alexavoicu/TSC-Proiect/Images/Baterie1.png

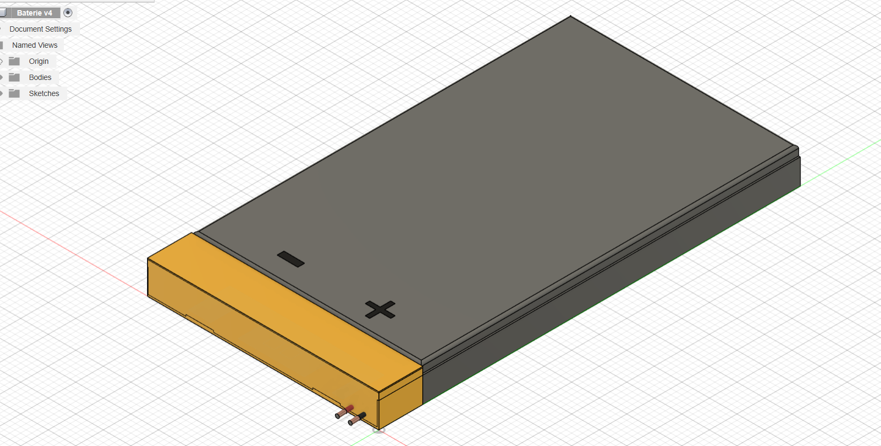
Images/Baterie1.png
