alexavoicu/TSC-Proiect/Images/Baterie2.png

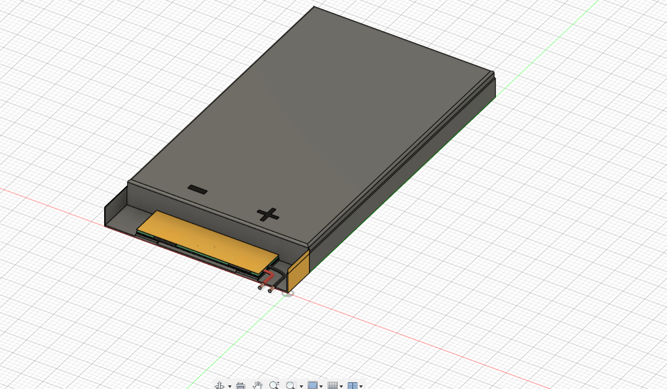
Images/Baterie2.png
