alexavoicu/TSC-Proiect/Images/Openbook2.png

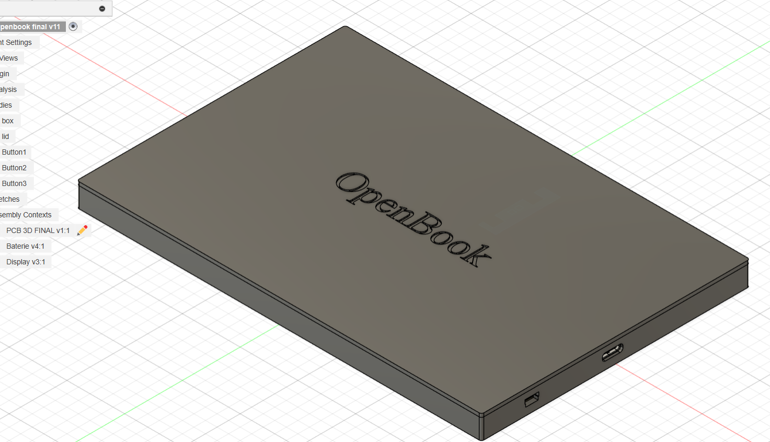
Images/Openbook2.png
