alexavoicu/TSC-Proiect/Images/Openbook3.png

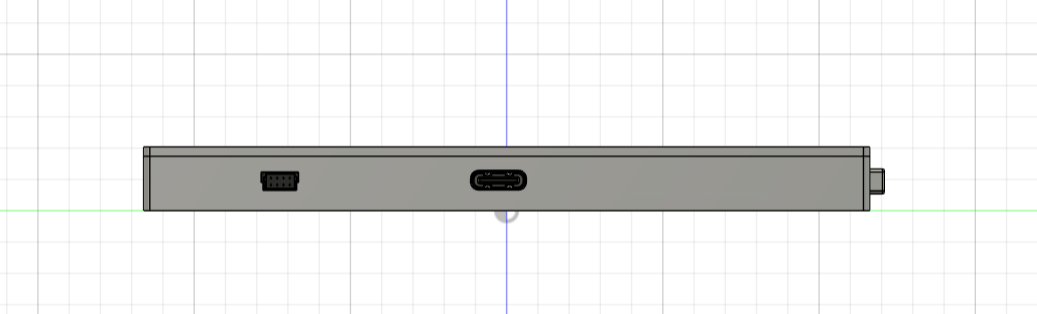
Images/Openbook3.png
