alexavoicu/TSC-Proiect/Images/Openbook5.png

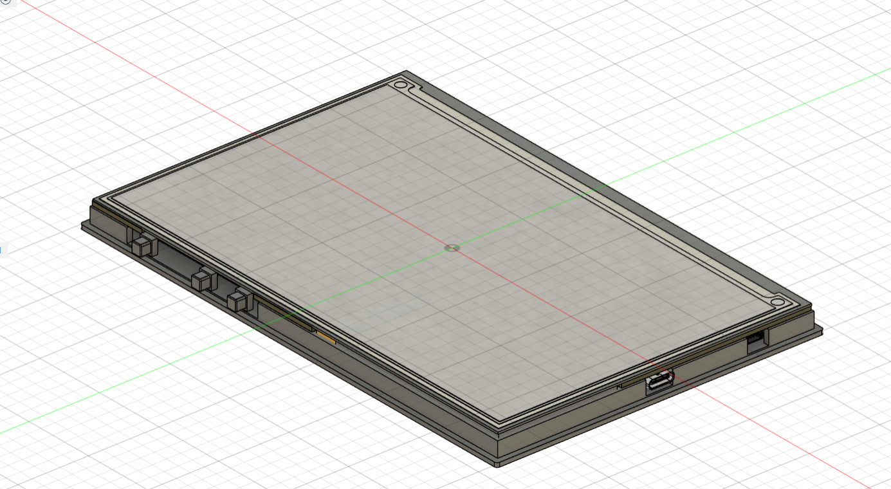
Images/Openbook5.png
