alexavoicu/TSC-Proiect/Images/PCB 3d1.png

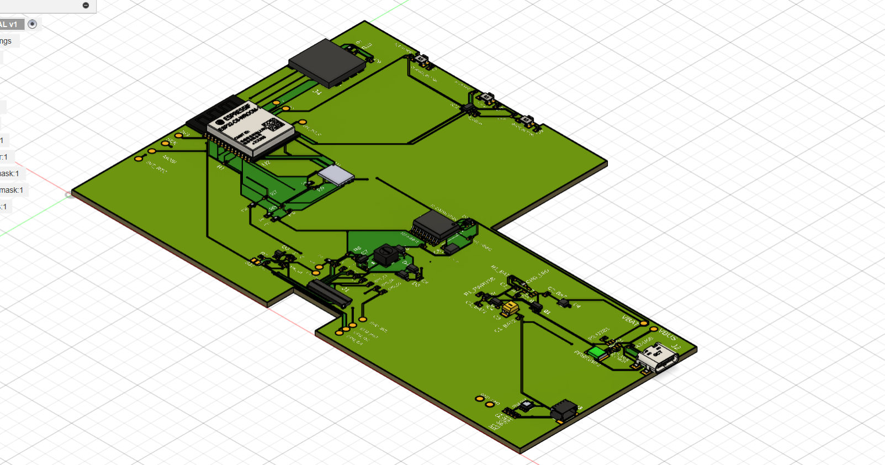
Images/PCB 3d1.png
