alexavoicu/TSC-Proiect/Images/PCB 3d2.png

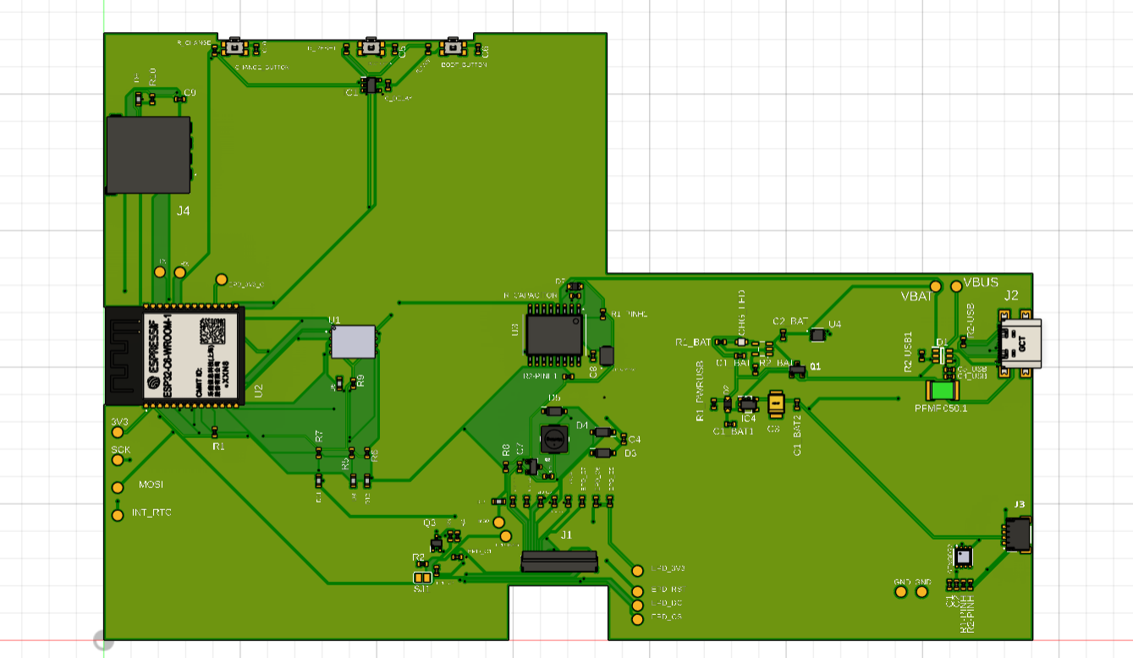
Images/PCB 3d2.png
